madworm/LED-strip_PWM_IR/gerber_files/PNGs/LED-strip_PWM_IR-B_Cu.gbl.png

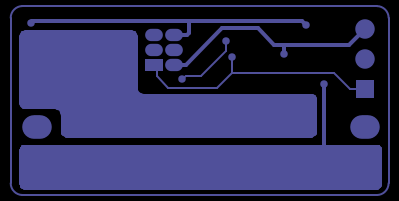
gerber_files/PNGs/LED-strip_PWM_IR-B_Cu.gbl.png
