madworm/LED-strip_PWM_IR/gerber_files/PNGs/LED-strip_PWM_IR-B_SilkS.gbo.png

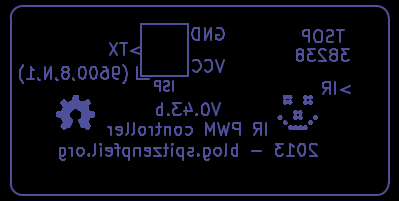
gerber_files/PNGs/LED-strip_PWM_IR-B_SilkS.gbo.png
