madworm/LED-strip_PWM_IR/gerber_files/PNGs/LED-strip_PWM_IR-F_Mask.gts.png

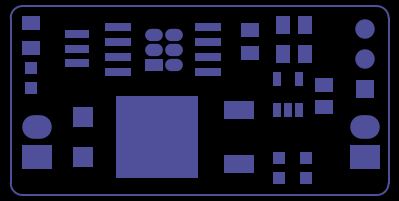
gerber_files/PNGs/LED-strip_PWM_IR-F_Mask.gts.png
