madworm/LED-strip_PWM_IR/gerber_files/PNGs/LED-strip_PWM_IR.drl.png

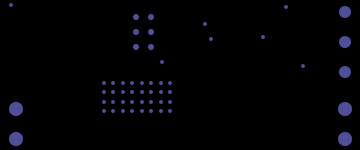
gerber_files/PNGs/LED-strip_PWM_IR.drl.png
