madworm/LED-strip_PWM_IR/gerber_files/PNGs/LED-strip_PWM_IR.png

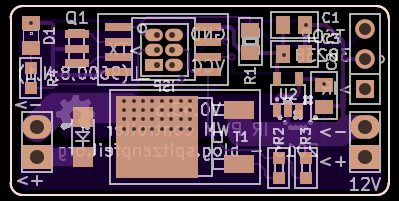
gerber_files/PNGs/LED-strip_PWM_IR.png
