madworm/LED-strip_PWM_IR/gerber_files/PNGs/LED-strip_PWM_IR__back_purple.png

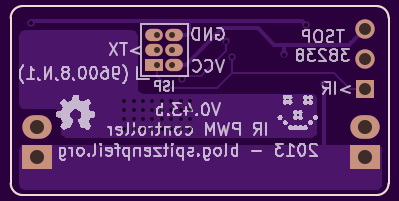
gerber_files/PNGs/LED-strip_PWM_IR__back_purple.png
